MATTMCCA/Salem-V3/cover_photos/000.png

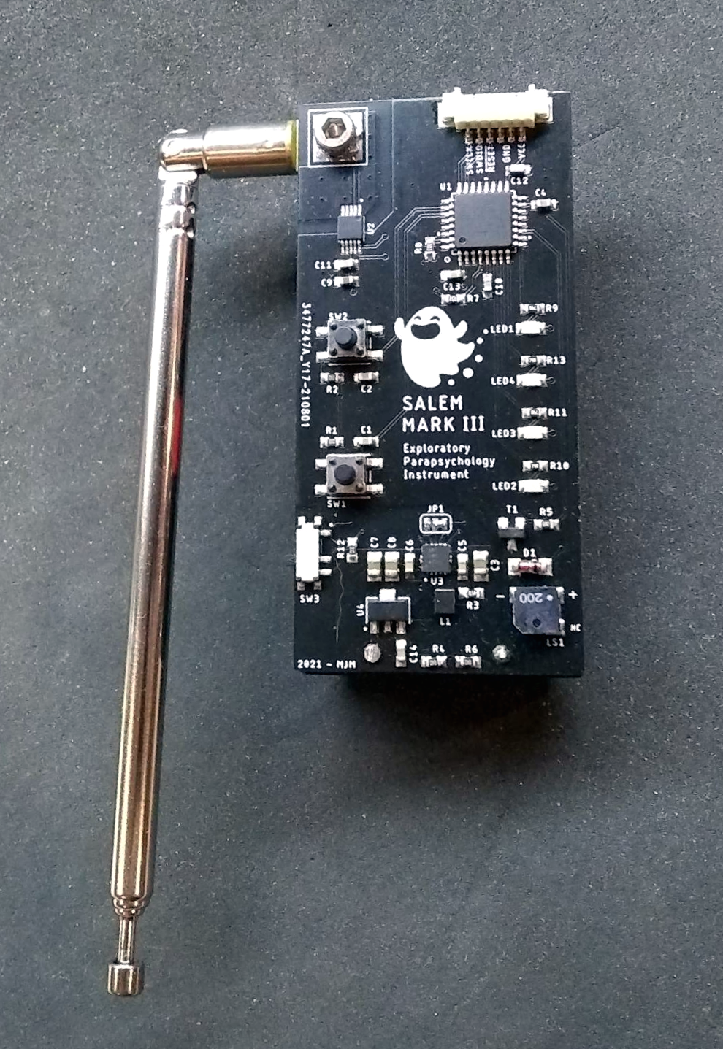
cover_photos/000.png
