MATTMCCA/Salem-V3/cover_photos/001.png

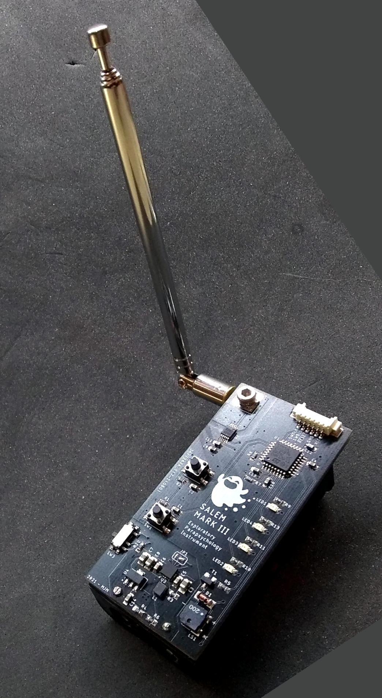
cover_photos/001.png
