MATTMCCA/Salem-V3/Datasheets/37cm 5 Section Telescopic Antenna/1Pc-37cm-5-Section-Telescopic-Stainless-Steel-Antenna.jpg_Q90.png

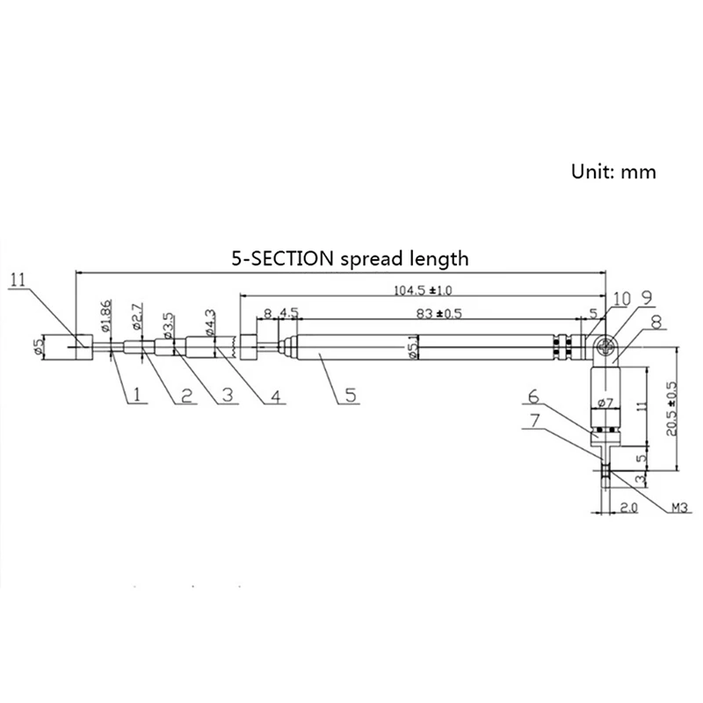
Datasheets/37cm 5 Section Telescopic Antenna/1Pc-37cm-5-Section-Telescopic-Stainless-Steel-Antenna.jpg_Q90.png
