MATTMCCA/Salem-V3/Hardware/Prog_Adapter/board/adapter_bot.png

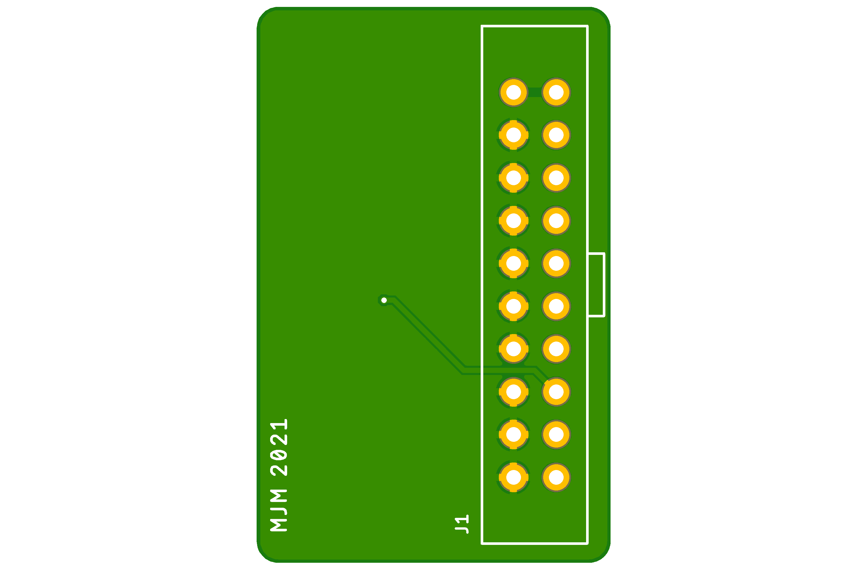
Hardware/Prog_Adapter/board/adapter_bot.png
