MATTMCCA/Salem-V3/Hardware/Prog_Adapter/board/adapter_top.png

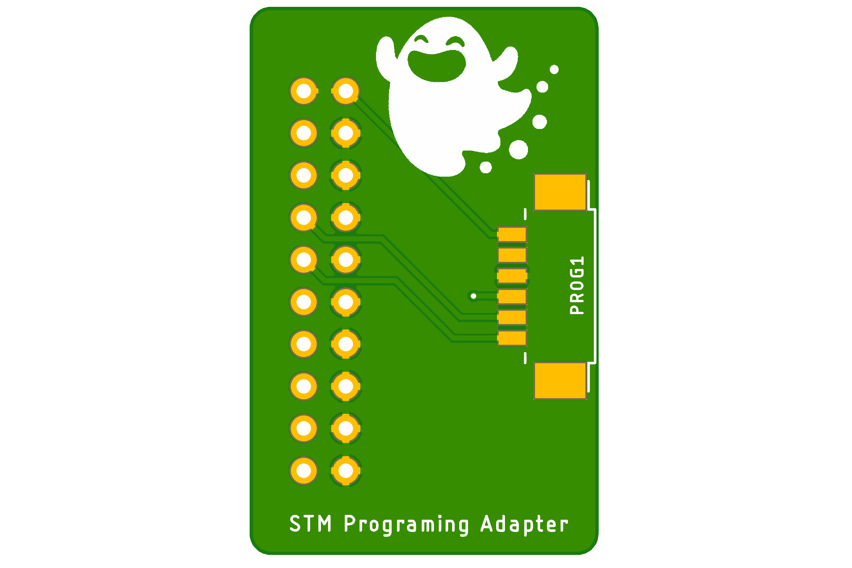
Hardware/Prog_Adapter/board/adapter_top.png
