MATTMCCA/Salem-V3/Hardware/SV3/board/SV3_top.png

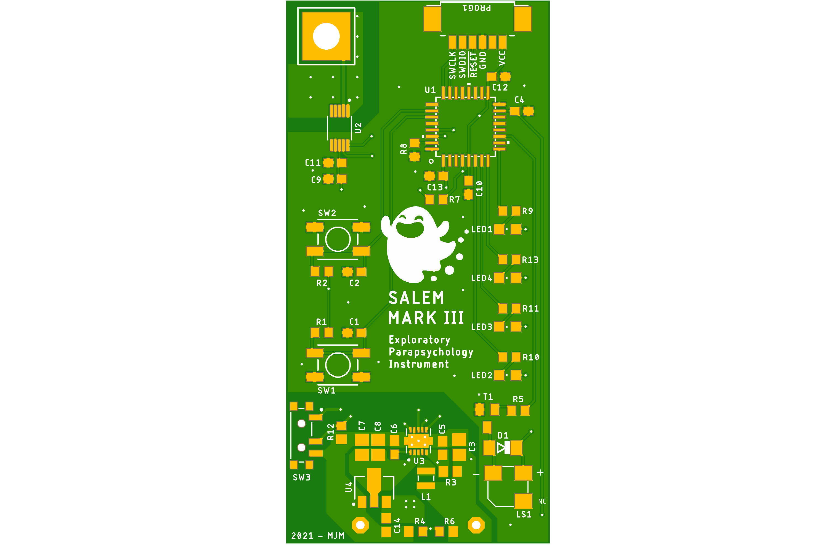
Hardware/SV3/board/SV3_top.png
