MATTMCCA/Salem-V3/Render/Pics/SV3 v5 001.png

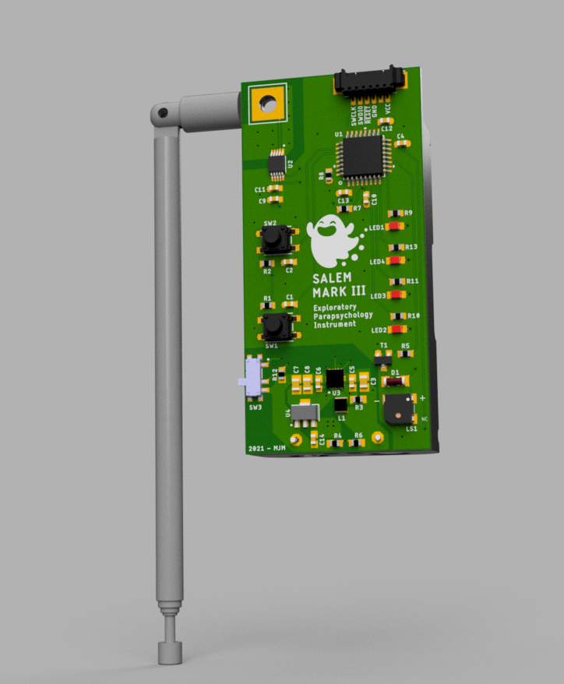
Render/Pics/SV3 v5 001.png
