MATTMCCA/Salem-V3/Manual/masters/pics/SV3 v4.png

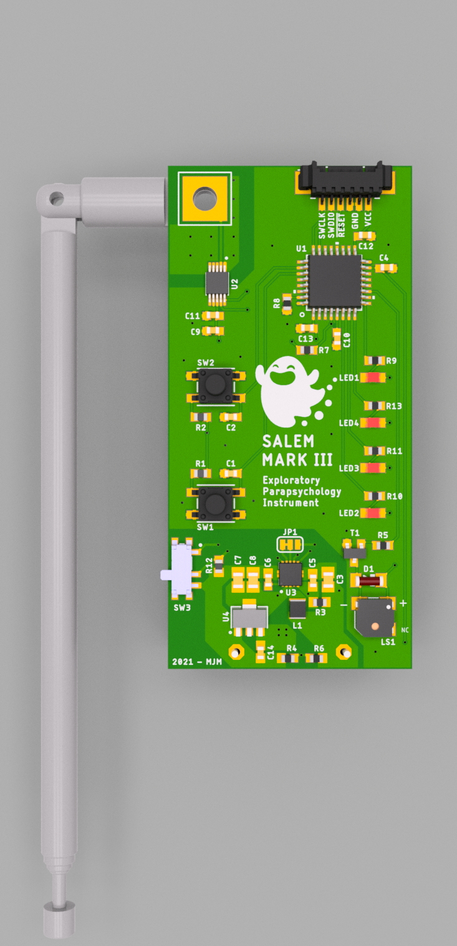
Manual/masters/pics/SV3 v4.png
