MATTMCCA/Salem-V3/SV3_Pics/other/field_test.png

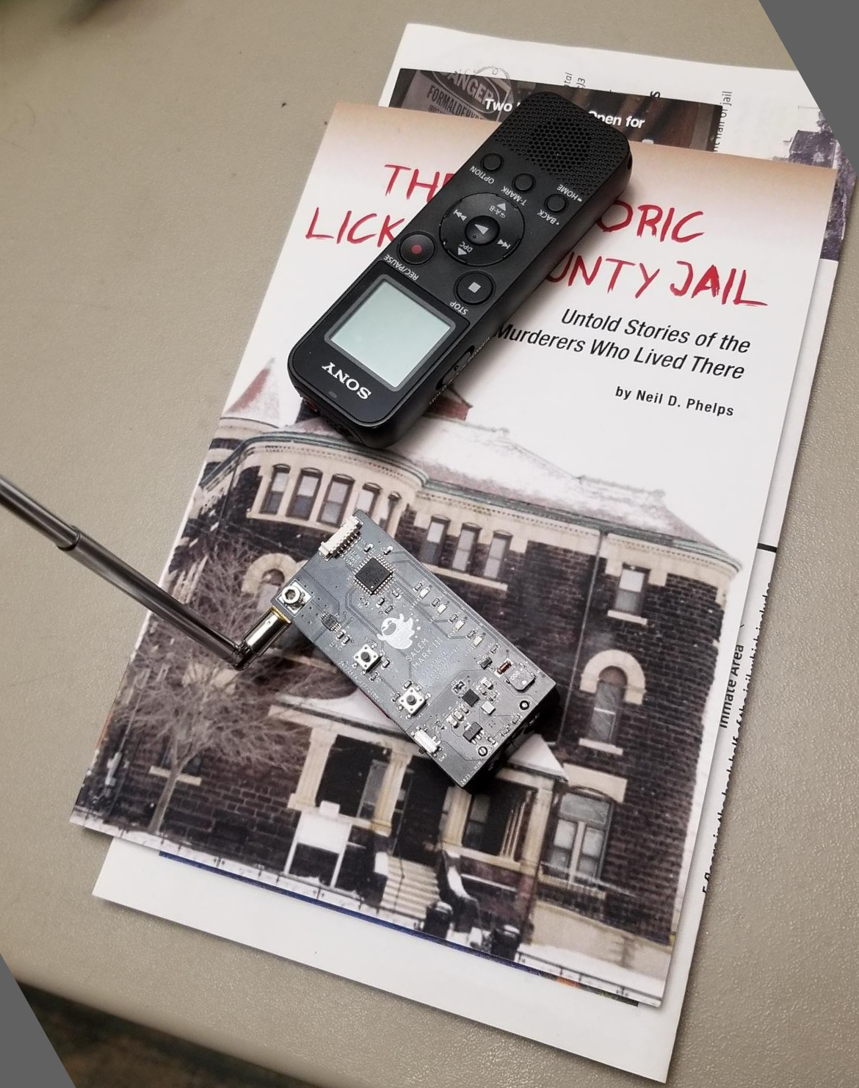
SV3_Pics/other/field_test.png
