MATTMCCA/Salem-V3/SV3_Pics/other/field_test_edit.jpg

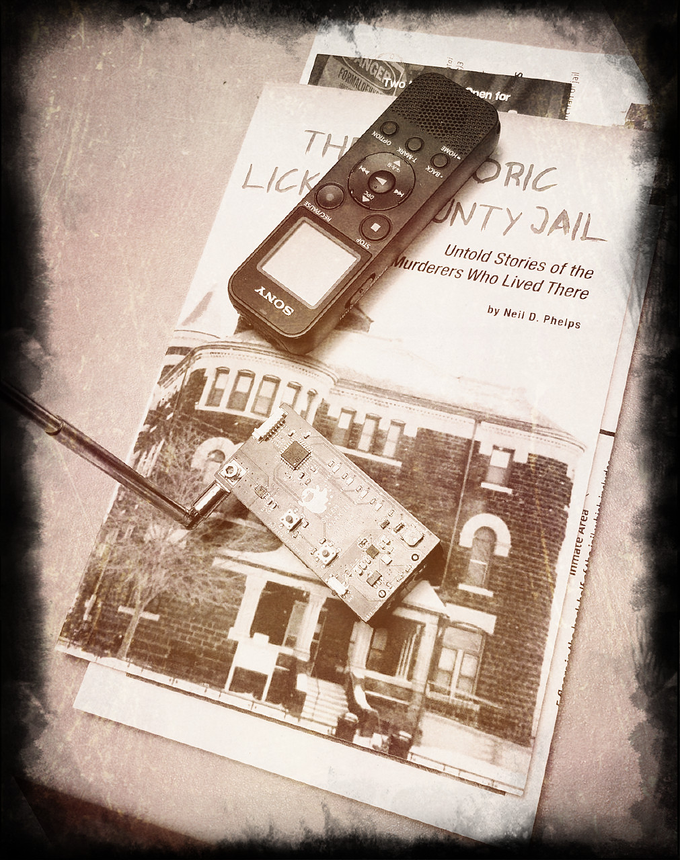
SV3_Pics/other/field_test_edit.jpg
